kverbeeck/IoT_Project_Line_Following_Car/Photos/New Design/IMG_9738.jpg

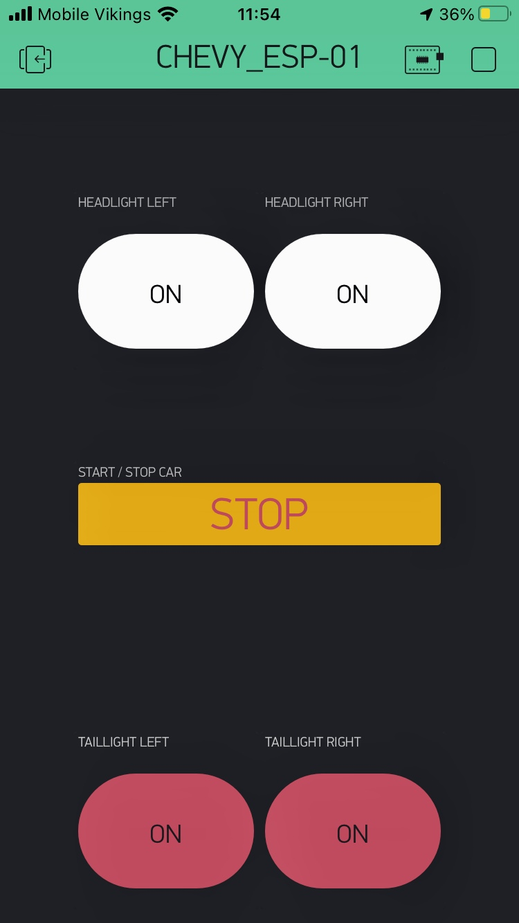
Photos/New Design/IMG_9738.jpg
