kverbeeck/IoT_Project_Line_Following_Car/Photos/New Design/Screen Shot 2021-05-30 at 11.18.38.png

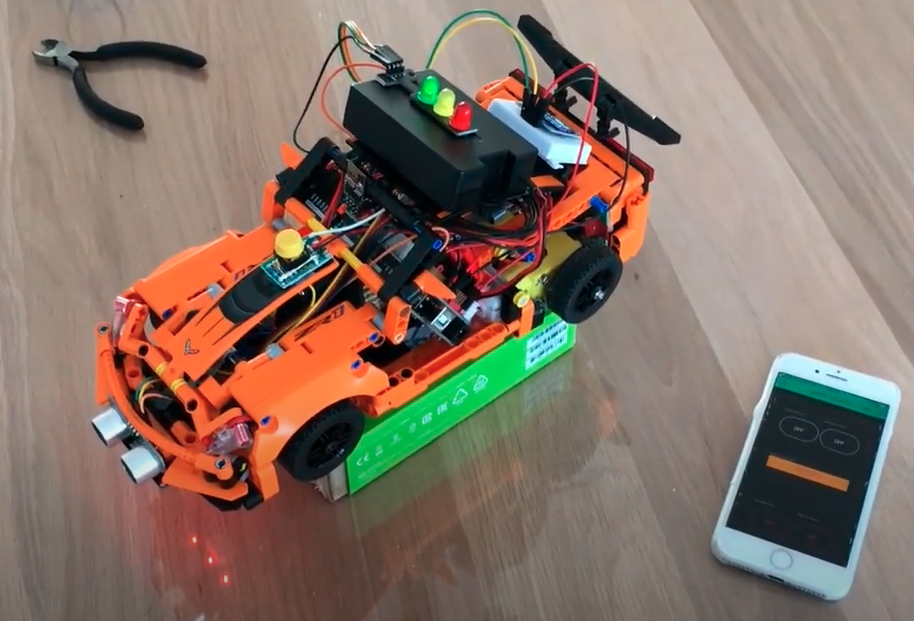
Photos/New Design/Screen Shot 2021-05-30 at 11.18.38.png
