kverbeeck/IoT_Project_Line_Following_Car/Schematics/Eagle - PCB Design.png

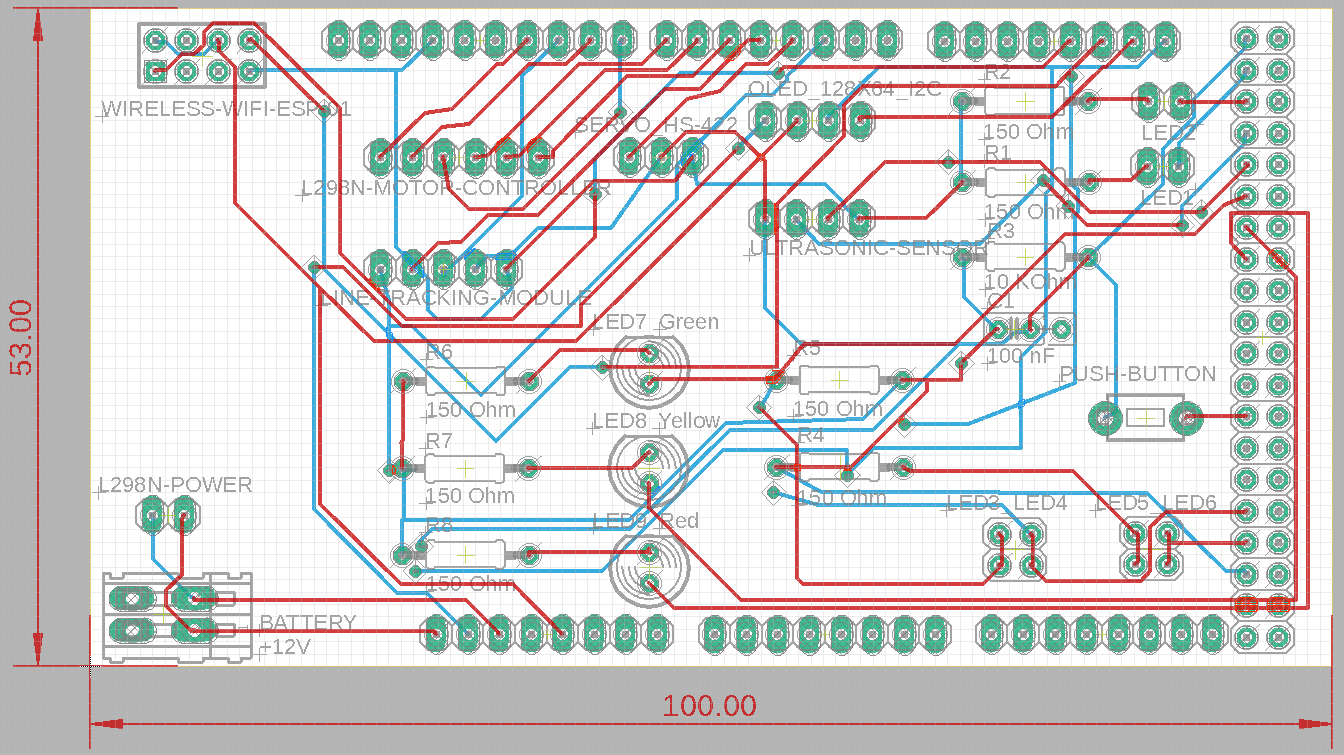
Schematics/Eagle - PCB Design.png
