kverbeeck/IoT_Project_Line_Following_Car/Schematics/Eagle - Schematic - Botom.png

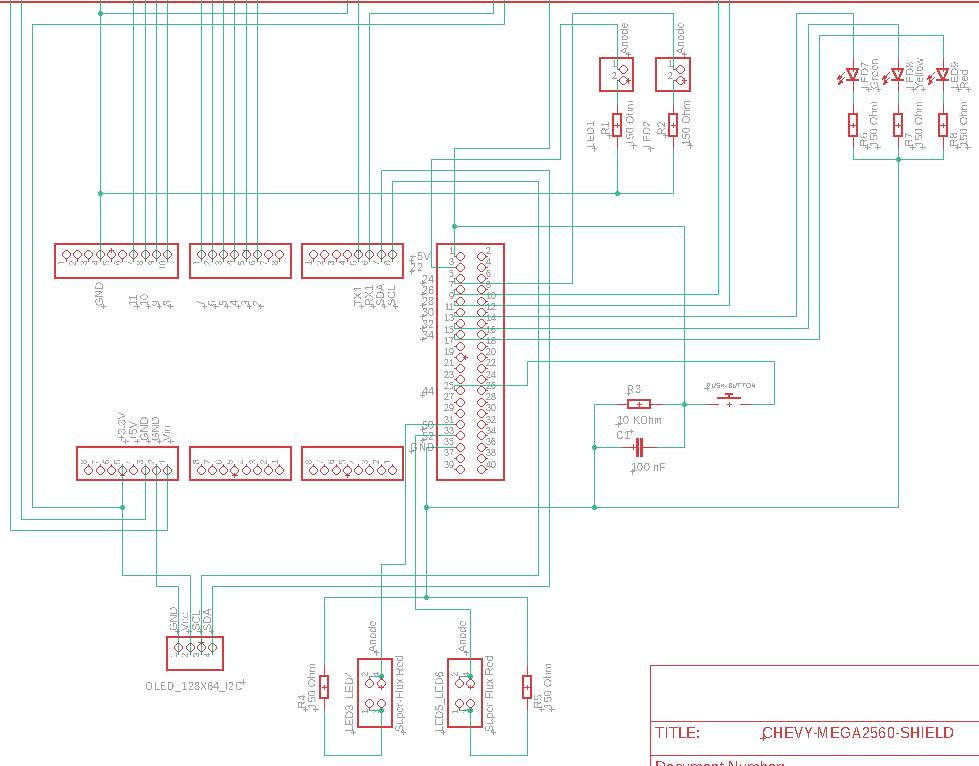
Schematics/Eagle - Schematic - Botom.png
