kverbeeck/IoT_Project_Line_Following_Car/Schematics/Eagle - Schematic - Top.png

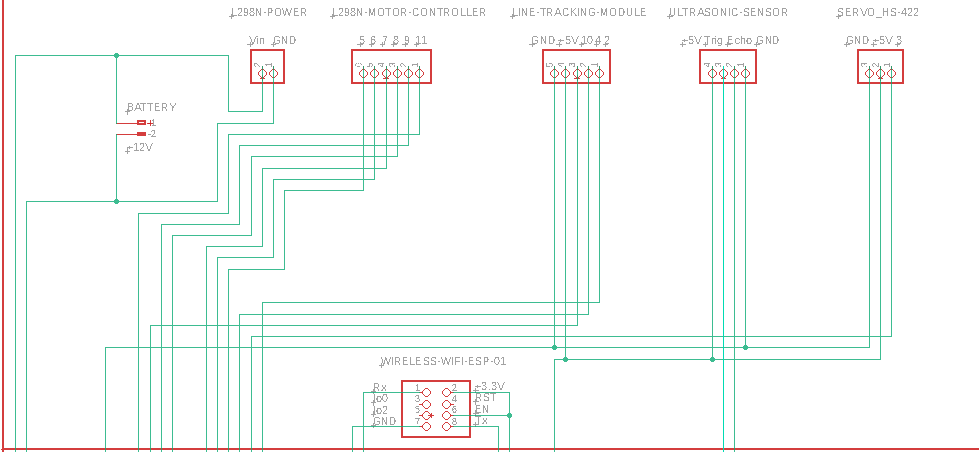
Schematics/Eagle - Schematic - Top.png
