kverbeeck/IoT_Project_Line_Following_Car/Schematics/Eagle - Schematic - Total.png

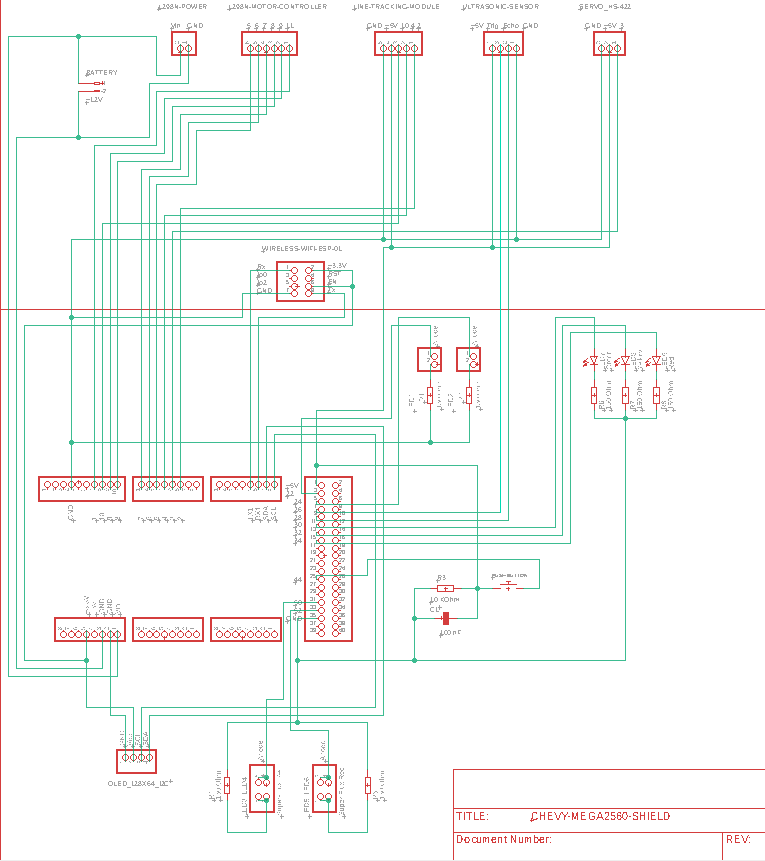
Schematics/Eagle - Schematic - Total.png
