kverbeeck/IoT_Project_Line_Following_Car/Schematics/Eagle Settings PCB Design/Screen Shot 2021-05-28 at 14.16.54.png

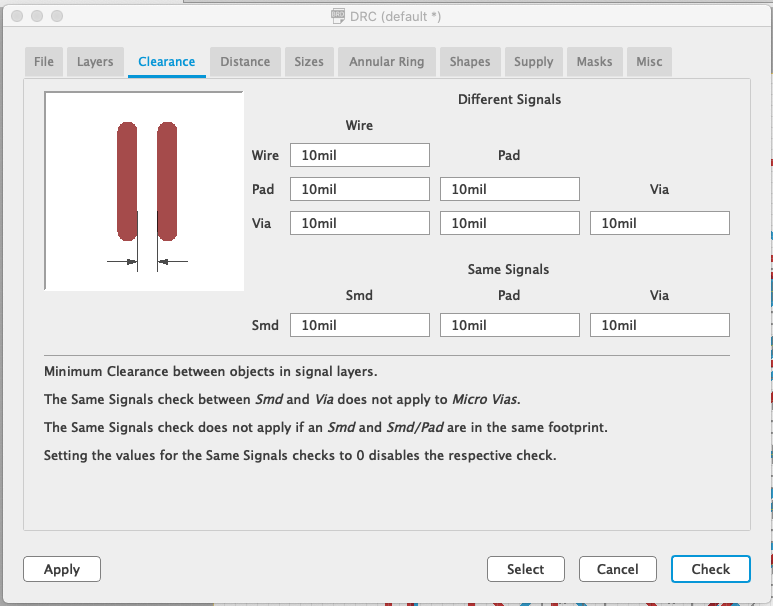
Schematics/Eagle Settings PCB Design/Screen Shot 2021-05-28 at 14.16.54.png
