kverbeeck/IoT_Project_Line_Following_Car/Schematics/Eagle Settings PCB Design/Screen Shot 2021-05-29 at 13.22.56.png

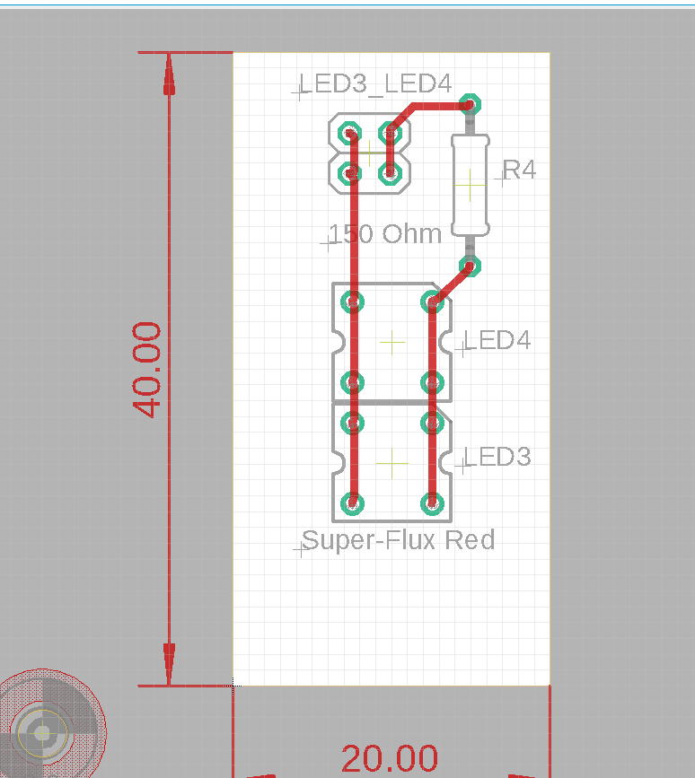
Schematics/Eagle Settings PCB Design/Screen Shot 2021-05-29 at 13.22.56.png
