kverbeeck/IoT_Project_Line_Following_Car/Schematics/Fritzing - Schematic.png

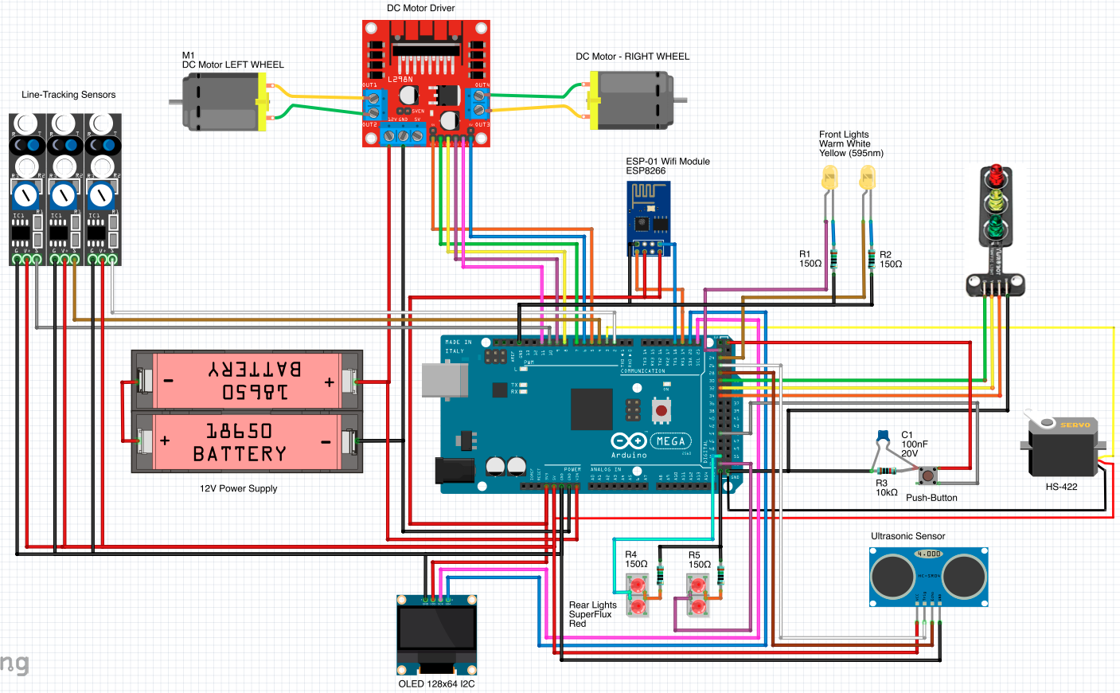
Schematics/Fritzing - Schematic.png
