kverbeeck/IoT_Project_Line_Following_Car/Schematics/PCB_CHEVY_Front.png

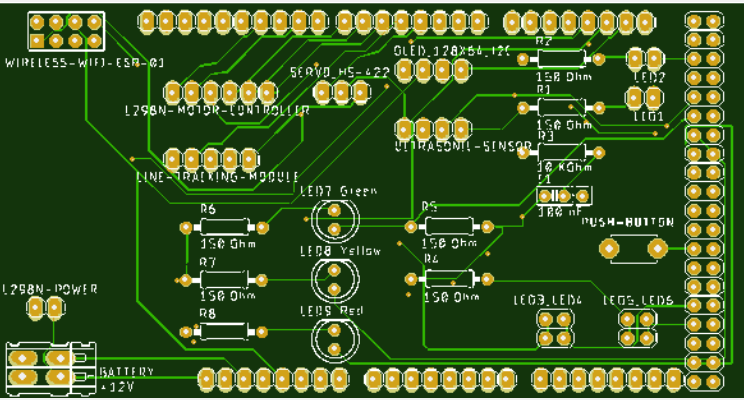
Schematics/PCB_CHEVY_Front.png
