kverbeeck/IoT_Project_Line_Following_Car/Schematics/PCB_LEFT_Backlight_Front.png

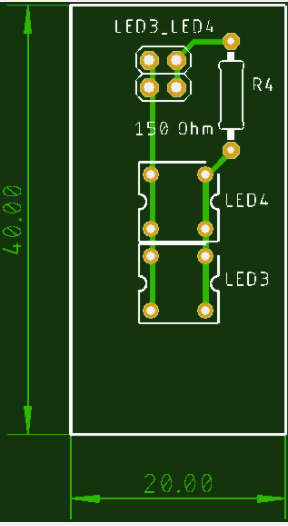
Schematics/PCB_LEFT_Backlight_Front.png
