kverbeeck/IoT_Project_Line_Following_Car/Schematics/PCB_OLED_Back.png

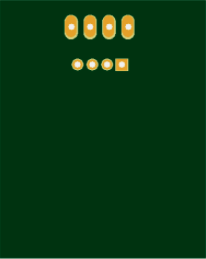
Schematics/PCB_OLED_Back.png
