kverbeeck/IoT_Project_Line_Following_Car/Schematics/PCB_OLED_Front.png

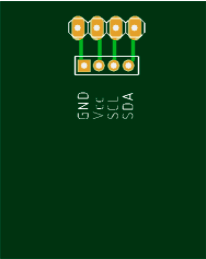
Schematics/PCB_OLED_Front.png
