kverbeeck/IoT_Project_Line_Following_Car/Schematics/Screen Shot 2021-05-27 at 17.02.21.png

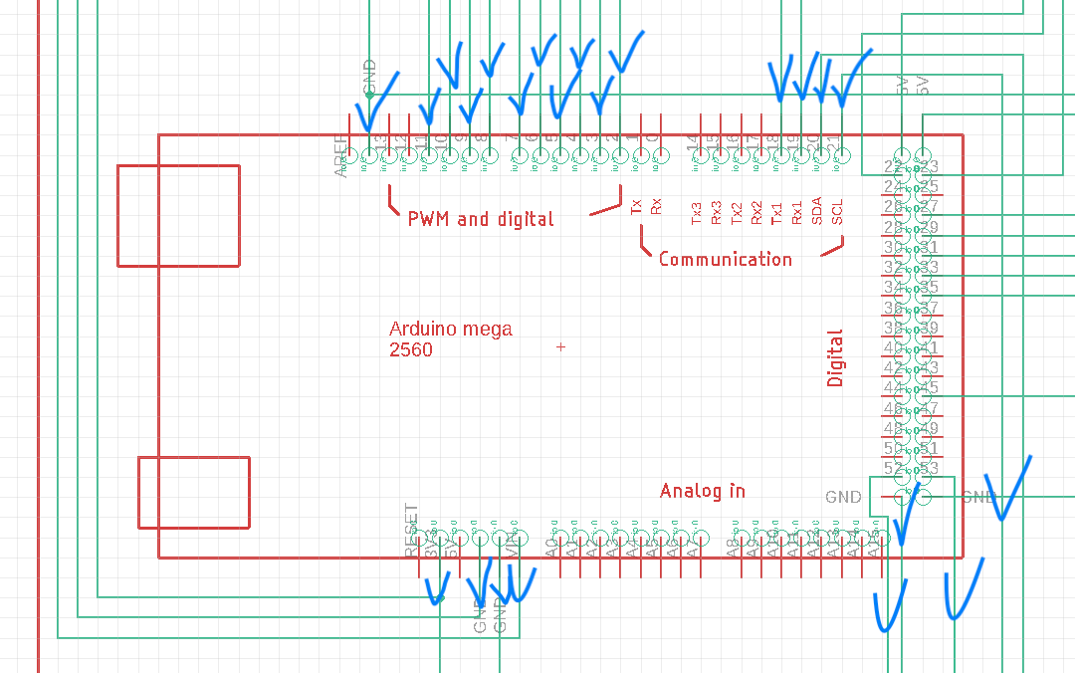
Schematics/Screen Shot 2021-05-27 at 17.02.21.png
