kverbeeck/IoT_Project_Line_Following_Car/Schematics/Screen Shot 2021-05-30 at 16.03.12.png

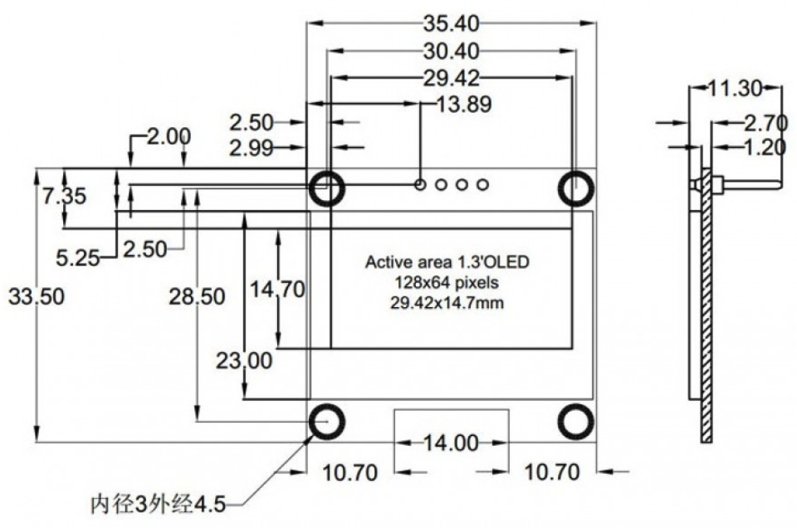
Schematics/Screen Shot 2021-05-30 at 16.03.12.png
