kverbeeck/IoT_Project_Line_Following_Car/3D_Printing/Screen Shot 2021-05-25 at 12.10.36.png

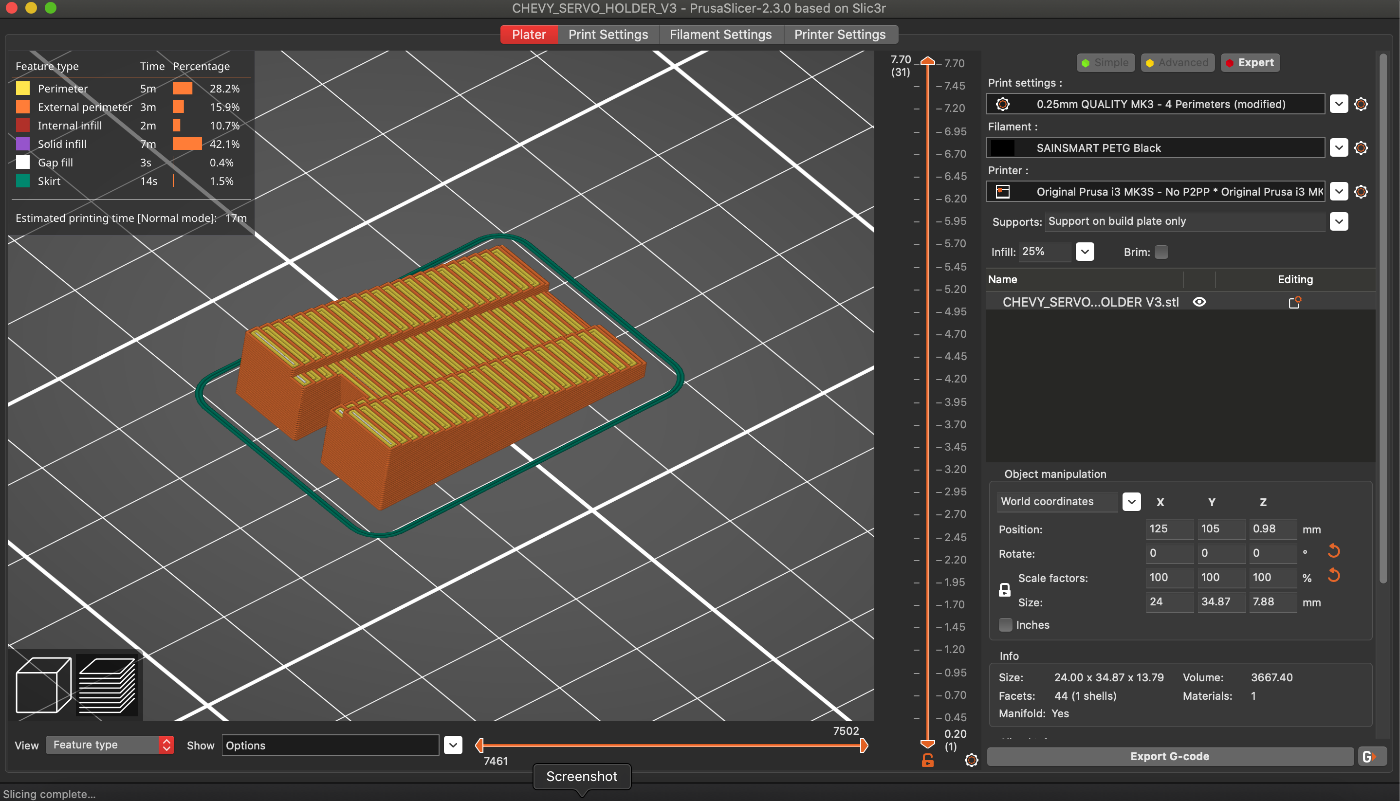
3D_Printing/Screen Shot 2021-05-25 at 12.10.36.png
